FlorianLa/BrailleBuddy/GermanVersion/GameModeCards/WordCards/Relief/Wortkarte links Uhr.stl

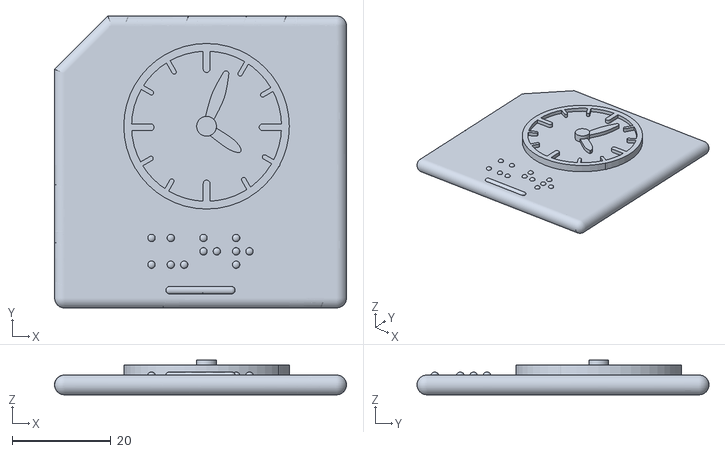
[picture p15: CAD file, 2023-01-21]
GermanVersion/GameModeCards/WordCards/Relief/Wortkarte links Uhr.stl
59.0 x 59.0 x 7.00
