FlorianLa/BrailleBuddy/GermanVersion/GameModeCards/WordCards/Relief/Wortkarte links Libelle.stl

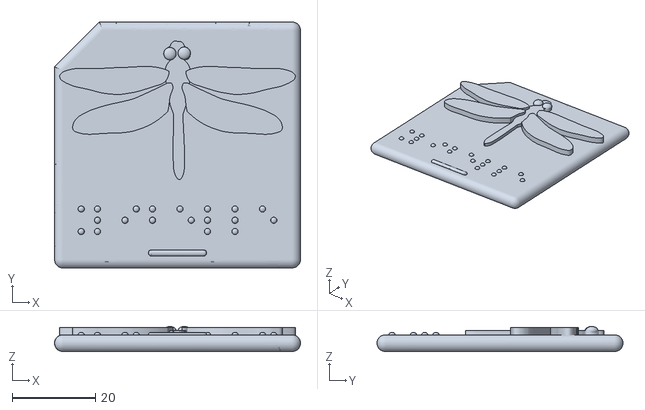
[picture p16: CAD file, 2023-01-21]
GermanVersion/GameModeCards/WordCards/Relief/Wortkarte links Libelle.stl
59.0 x 59.0 x 6.00
