FlorianLa/BrailleBuddy/GermanVersion/GameModeCards/WordCards/Relief/Wortkarte links Globus.stl

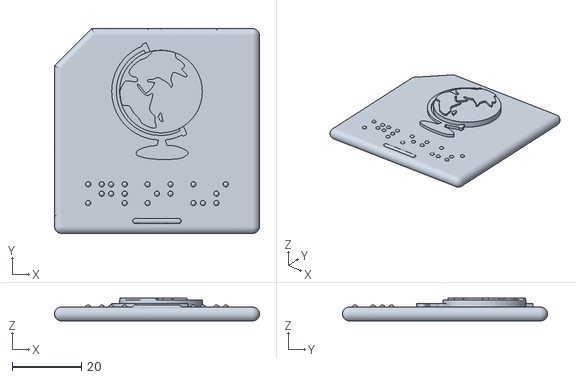
[picture p17: CAD file, 2023-01-21]
GermanVersion/GameModeCards/WordCards/Relief/Wortkarte links Globus.stl
59.0 x 59.0 x 6.60
