FlorianLa/BrailleBuddy/GermanVersion/GameModeCards/WordCards/Relief/Wortkarte links Dreieck.stl

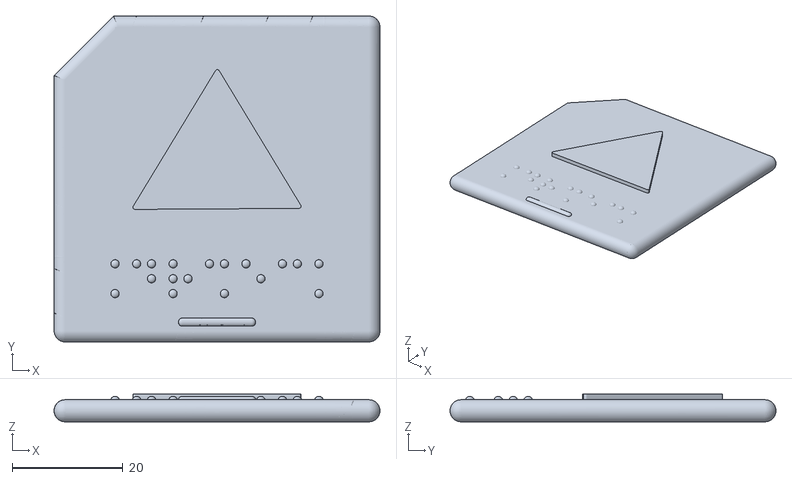
[picture p18: CAD file, 2023-01-21]
GermanVersion/GameModeCards/WordCards/Relief/Wortkarte links Dreieck.stl
59.0 x 59.0 x 5.00
