FlorianLa/BrailleBuddy/GermanVersion/GameModeCards/WordCards/Relief/Wortkarte links Pfote.stl

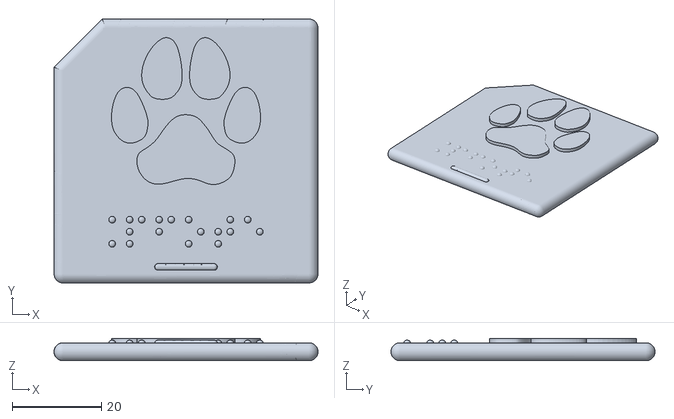
[picture p19: CAD file, 2023-01-21]
GermanVersion/GameModeCards/WordCards/Relief/Wortkarte links Pfote.stl
59.0 x 59.0 x 5.00
