FlorianLa/BrailleBuddy/GermanVersion/GameModeCards/WordCards/Relief/Wortkarte links Elefant 2D.stl

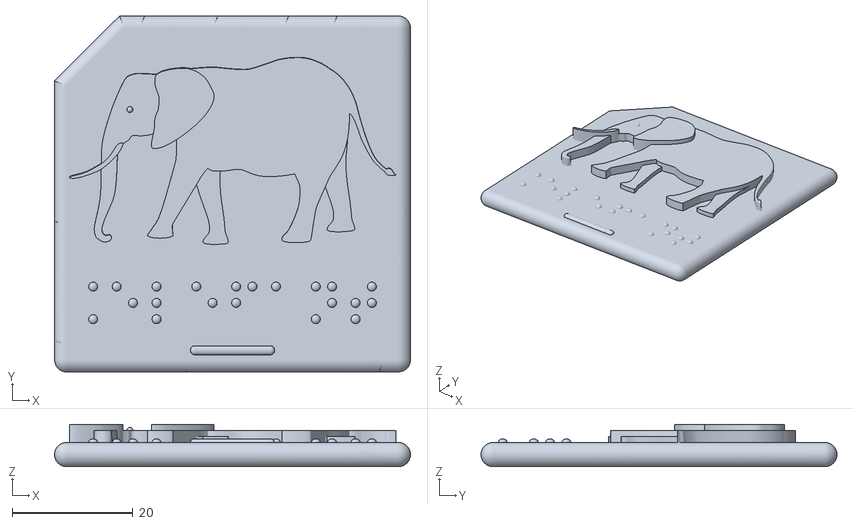
[picture p26: CAD file, 2023-01-21]
GermanVersion/GameModeCards/WordCards/Relief/Wortkarte links Elefant 2D.stl
59.0 x 59.0 x 7.00
